AlessandroBelfiore257/BlackBoxProject/img/ClusterizzazioneG.jpg

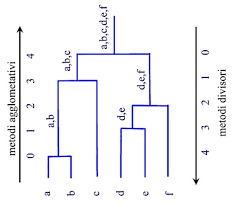
img/ClusterizzazioneG.jpg
