AlessandroBelfiore257/BlackBoxProject/src/Garbage.cpp

#include "Garbage.h"

extern sqlite3* db;

/*
  Descrizione: restituisce il numero di record presenti dentro la tabella t1 (monitoraggio)
  Input: db, ovvero il database in cui sono memorizzati i dati
  Return: il numero di record presenti all'interno di t1
*/
int countRecordsInTableMonitoring(sqlite3* db) {
  int count = 0;
  char* sql = "SELECT COUNT(*) FROM t1;";
  char** result;
  int rows, columns;
  char* errMsg = 0;

  int rc = sqlite3_get_table(db, sql, &result, &rows, &columns, &errMsg);
  if (rc == SQLITE_OK) {
    // Il risultato della query è memorizzato in result[1]
    // Converto il valore restituito da stringa a intero
    count = atoi(result[1]);
    sqlite3_free_table(result);
  } else {
    #ifdef DEBUG
    Serial.print("SQL error: ");
    Serial.println(errMsg);
    #endif
    sqlite3_free(errMsg);
  }
  return count;
}

/*
  Descrizione: elimina i primi x record più datati presenti all'interno della tabella t1 
  Input: 
    - db, ovvero il database in cui sono memorizzati i dati
    - x, il numero di record da eliminare 
  Return: void
*/
void deleteFirstXRecords(sqlite3* db, int x) {
  char selectSql[BUFFER_SIZE];
  char deleteSql[BUFFER_SIZE];
  snprintf(selectSql, sizeof(selectSql), "SELECT rowid FROM t1 ORDER BY timestamp ASC LIMIT %d;", x);
  int rc = db_exec(db, "BEGIN TRANSACTION;");
  if (rc != SQLITE_OK) {
    Serial.println("Error starting transaction.");
    return;
  }
  std::vector<int> rowids;
  sqlite3_stmt* stmt;
  rc = sqlite3_prepare_v2(db, selectSql, -1, &stmt, 0);
  if (rc == SQLITE_OK) {
    while (sqlite3_step(stmt) == SQLITE_ROW) {
      int rowid = sqlite3_column_int(stmt, 0);
      rowids.push_back(rowid);
    }
    sqlite3_finalize(stmt);
  } else {
    #ifdef DEBUG
    Serial.println("Error selecting rowids.");
    #endif
    db_exec(db, "ROLLBACK;");
    return;
  }
  if (!rowids.empty()) {
    String ids;
    for (int id : rowids) {
      ids += String(id) + ",";
    }
    ids.remove(ids.length() - 1);  
    snprintf(deleteSql, sizeof(deleteSql), "DELETE FROM t WHERE rowid IN (%s);", ids.c_str());
    rc = db_exec(db, deleteSql);
    if (rc != SQLITE_OK) {
      #ifdef DEBUG
      Serial.println("Error deleting records.");
      #endif
      db_exec(db, "ROLLBACK;");
    } else {
      rc = db_exec(db, "COMMIT;");
      if (rc != SQLITE_OK) {
        #ifdef DEBUG
        Serial.println("Error committing changes.");
        #endif
        db_exec(db, "ROLLBACK;");
      } else {
        #ifdef DEBUG
        Serial.println("Records deleted successfully.");
        #endif
      }
    }
  } else {
    #ifdef DEBUG
    Serial.println("No records to delete.");
    #endif
    db_exec(db, "ROLLBACK;");
  }
}

void garbageCollectorRoutine() {
  if (db_open(PATH_STORAGE_DATA_DB, &db))
    return;
  int rc = db_exec(db, "BEGIN TRANSACTION;");
  if (rc != SQLITE_OK) {
    #ifdef DEBUG
    Serial.println("Error starting transaction.");
    #endif
    sqlite3_close(db);
    return;
  }
  char* sql = "DELETE FROM t1 WHERE synchronised = 1;";
  rc = db_exec(db, sql);
  if (rc != SQLITE_OK) {
    #ifdef DEBUG
    Serial.println("Error cleaning synced data.");
    #endif
    db_exec(db, "ROLLBACK;");
  } else {
    rc = db_exec(db, "COMMIT;");
    if (rc != SQLITE_OK) {
      #ifdef DEBUG
      Serial.println("Error committing changes.");
      #endif
      db_exec(db, "ROLLBACK;");
    } else {
      #ifdef DEBUG
      Serial.println("Synced data cleaned successfully.");
      #endif
      rc = db_exec(db, "VACUUM;");
      if (rc != SQLITE_OK) {
        #ifdef DEBUG
        Serial.println("Error vacuuming database.");
        #endif
      } else {
        #ifdef DEBUG
        Serial.println("Database vacuumed successfully.");
        #endif
      }
      rc = db_exec(db, "PRAGMA wal_checkpoint(FULL);");
      if (rc != SQLITE_OK) {
        #ifdef DEBUG
        Serial.println("Error checkpointing WAL.");
        #endif
      }
      rc = db_exec(db, "PRAGMA shrink_memory;");
      if (rc != SQLITE_OK) {
        #ifdef DEBUG
        Serial.println("Error shrinking memory.");
        #endif
      }
    }
  }
  sqlite3_close(db);
}

void garbageCollectorMemoryFull() {
  if (db_open(PATH_STORAGE_DATA_DB, &db))
    return;

  int numRecordPre = countRecordsInTableMonitoring(db);
  int recordToDelete = numRecordPre / 2;
  #ifdef DEBUG
  Serial.print("Record totali: ");
  Serial.println(numRecordPre);
  Serial.print("Record da eliminare: ");
  Serial.println(recordToDelete);
  #endif
  // In primis elimino i record già sincronizzati
  garbageCollectorRoutine();
  if (db_open("/littlefs/dati.db", &db))
    return;
  int numRecordPost = countRecordsInTableMonitoring(db);
  // Sono i record rimanti da eliminare
  int res = numRecordPost - recordToDelete;
  #ifdef DEBUG
  Serial.print("Record rimasti: ");
  Serial.println(numRecordPost);
  Serial.print("Record rimasti da eliminare: ");
  Serial.println(res);
  #endif
  deleteFirstXRecords(db, res);
  sqlite3_close(db);
}

// ########################################### Profilazione ###########################################

/*
  Descrizione: conta il numero di voti registrati per la profilazione
  Input: db, ovvero il database in cui sono memorizzati i dati
  Return: il numero di voti registrati per profilare il conducente
*/
int countSyncedRecordsInT3(sqlite3* db) {
  const char* sql = "SELECT COUNT(*) FROM t3 WHERE synchronised = 1";
  sqlite3_stmt* stmt;
  int count = 0;
  if (db_open(PATH_STORAGE_DATA_DB, &db)) {
    #ifdef DEBUG
    Serial.println("Failed to open the database.");
    #endif
    return 0;
  }
  if (sqlite3_prepare_v2(db, sql, -1, &stmt, NULL) != SQLITE_OK) {
    #ifdef DEBUG
    Serial.printf("Failed to prepare statement: %s\n", sqlite3_errmsg(db));
    #endif
    sqlite3_close(db);
    return 0;
  }
  if (sqlite3_step(stmt) == SQLITE_ROW) {
    count = sqlite3_column_int(stmt, 0);
  }
  sqlite3_finalize(stmt);
  sqlite3_close(db);
  #ifdef DEBUG
  Serial.printf("Number of synced records: %d\n", count);
  #endif
  return count;
}

/*
  Descrizione: elimina i voti registrati in t3 (profilazione)
  Input: db, ovvero il database in cui sono memorizzati i dati
  Return: void 
*/
void deleteSyncedRecordsFromT3(sqlite3* db) {
  const char* sql = "DELETE FROM t3 WHERE synchronised = 1";

  if (db_open(PATH_STORAGE_DATA_DB, &db)) {
    #ifdef DEBUG
    Serial.println("Failed to open the database.");
    #endif
    return;
  }
  char* errMsg = 0;
  int rc = sqlite3_exec(db, sql, NULL, NULL, &errMsg);
  if (rc != SQLITE_OK) {
    #ifdef DEBUG
    Serial.printf("Failed to delete synced records: %s\n", errMsg);
    #endif
    sqlite3_free(errMsg);
  } else {
    #ifdef DEBUG
    Serial.println("Successfully deleted synced records.");
    #endif
  }
  sqlite3_close(db);
}

void eliminazioneVotiProfilazione(sqlite3* db) {
  if (countSyncedRecordsInT3(db) > CLEAN_PROFILAZIONE_DAY) {  // significa che sono passati 30 giorni dato che il voto sarà registrato al max una volta al giorno
    deleteSyncedRecordsFromT3(db);
  }
}

// ########################################### Allarmi rossi ###########################################

void cleanAllarmiRed(sqlite3* db) {
  const char* sql = "DELETE FROM t4 WHERE synchronised = 1";
  if (db_open(PATH_STORAGE_DATA_DB, &db)) {
    #ifdef DEBUG
    Serial.println("Failed to open the database.");
    #endif
    return;
  }
  char* errMsg = 0;
  int rc = sqlite3_exec(db, sql, NULL, NULL, &errMsg);
  if (rc != SQLITE_OK) {
    #ifdef DEBUG
    Serial.printf("Failed to delete synced records: %s\n", errMsg);
    #endif
    sqlite3_free(errMsg);
  } else {
    #ifdef DEBUG
    Serial.println("Successfully deleted synced records.");
    #endif
  }
  sqlite3_close(db);
}

// ########################################### Allarmi gialli ###########################################

// La frequeza di pulizia per questo particolare compito sarà molto lunga --> 7 giorni ad esempio
void cleanAllarmiYellow(sqlite3* db) {
  int rc = db_open(PATH_STORAGE_DATA_DB, &db);
  if (rc != SQLITE_OK) {
    #ifdef DEBUG
    Serial.println("Failed to open the database.");
    #endif
    return;
  }
  // Query SQL per aggiornare i campi "daMandare", "rilevamenti" e "synchronised" a 0 per tutti i record
  const char* sql = "UPDATE t5 SET daMandare = 0, rilevamenti = 0, synchronised = 0";
  char* errMsg = 0;
  rc = sqlite3_exec(db, sql, NULL, NULL, &errMsg);
  if (rc != SQLITE_OK) {
    #ifdef DEBUG
    Serial.printf("Failed to reset fields: %s\n", errMsg);
    #endif
    sqlite3_free(errMsg);
  } else {
    #ifdef DEBUG
    Serial.println("Successfully reset daMandare and rilevamenti for all records.");
    #endif
  }
  sqlite3_close(db);
}
